telzo2000/cool836qal/img/img00001.jpg

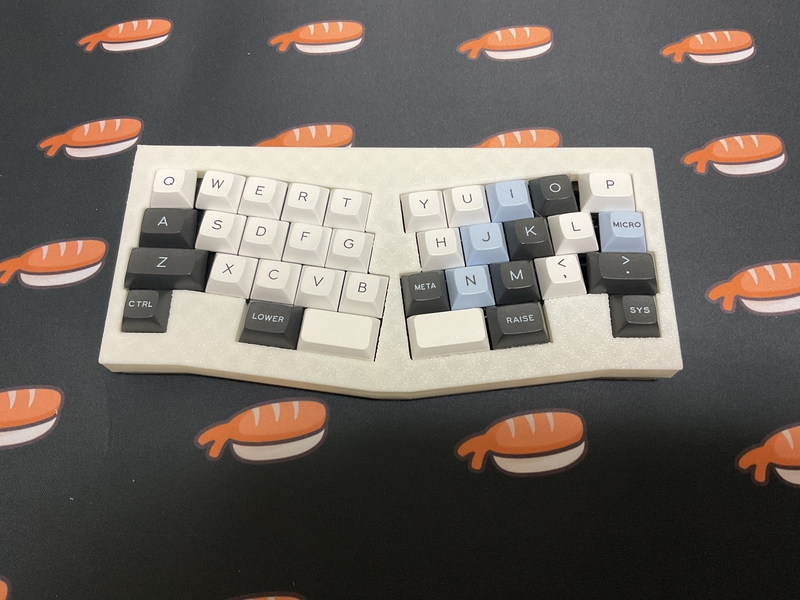
img/img00001.jpg
