telzo2000/cool836qal/img/img00011.jpg

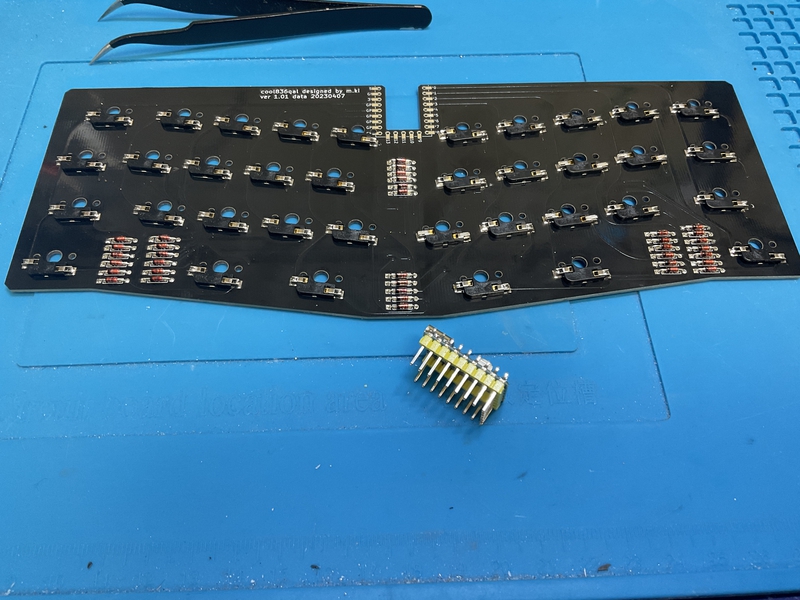
img/img00011.jpg
