telzo2000/cool836qal/img/img00012.jpg

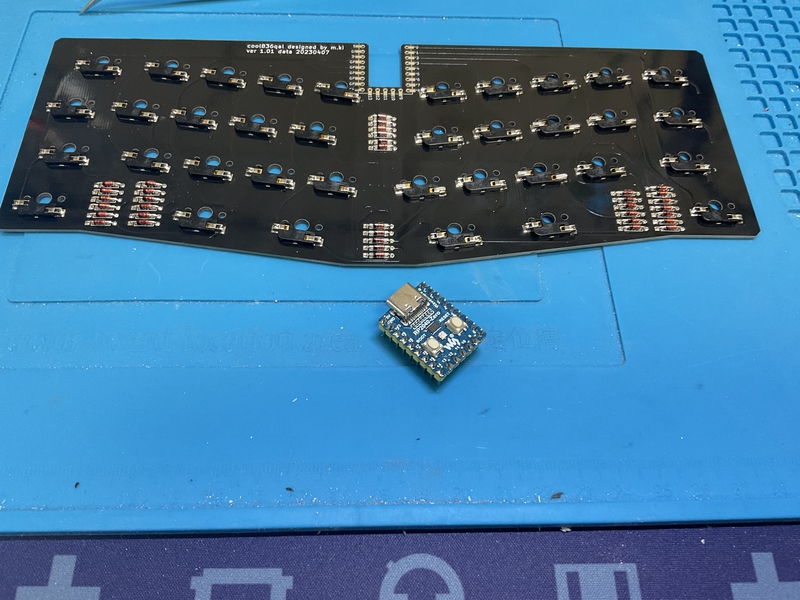
img/img00012.jpg
